No-Chicken/Power-Pico/software/bootloader/Core/Src/main.c

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
/* Includes ------------------------------------------------------------------*/
#include "main.h"
#include "crc.h"
#include "i2c.h"
#include "spi.h"
#include "tim.h"
#include "usb_device.h"
#include "gpio.h"

/* USER CODE BEGIN Includes */
#include <string.h>
#include <stdio.h>
#include "menu.h"
#include "common.h"
#include "delay.h"
#include "lcd.h"
#include "lcd_init.h"
#include "key.h"
#include "BL24C02.h"
/* USER CODE END Includes */


/* USER CODE BEGIN PV */

extern pFunction Jump_To_Application;
extern uint32_t JumpAddress;

/* USER CODE END PV */

void SystemClock_Config(void);
/* USER CODE BEGIN 0 */
void Bootloader_Main(void)
{
  // Bootloader 循环等待上位机指令
  while (1)
  {
      // 1. 发送握手信号
      USB_PutString("##PICO_BOOT##\r\n");
      // 2. 在延时期间(比如500ms)不断检查有没有收到数据
      // 这样既实现了延时，又不会阻塞接收
      uint8_t key = 0;
      for (int i = 0; i < 50; i++)
      {
          // USB_KeyPressed 应该是一个非阻塞检查函数
          // 如果收到数据返回 1，否则返回 0
          if (USB_KeyPressed(&key))
          {
              if (key == '0')
              {
                  // 收到 '0'，进入菜单
                  Main_Menu();
              }
          }
          HAL_Delay(10); // 每次只延时 10ms，检查 50 次 = 500ms
      }
  }
}
/* USER CODE END 0 */

/**
  * @brief  The application entry point.
  * @retval int
  */
int main(void)
{

  /* USER CODE BEGIN 1 */
	SCB->VTOR = FLASH_BASE;
  /* USER CODE END 1 */

  /* MCU Configuration--------------------------------------------------------*/

  /* Reset of all peripherals, Initializes the Flash interface and the Systick. */
  HAL_Init();

  /* Configure the system clock */
  SystemClock_Config();

  /* Initialize all configured peripherals */
  MX_GPIO_Init();
  MX_SPI2_Init();
  MX_TIM1_Init();
  MX_I2C1_Init();
  MX_USB_DEVICE_Init();
  MX_CRC_Init();
  /* USER CODE BEGIN 2 */

	//sys delay
	delay_init();

  //key_boot
	Key_Port_Init();

	// PWM Start for LCD backlight
	HAL_TIM_PWM_Start(&htim1, TIM_CHANNEL_3);

	//lcd
	LCD_Init();
	LCD_Fill(0, 0, LCD_W, LCD_H, BLACK);
	delay_ms(10);
	LCD_Set_Light(50);

	// extern eeprom BL24C02
	uint8_t update_flag = 0;
	if(!EEPROM_Init_Check()) {
		update_flag = EEPROM_UpdateCommand_Check();
		if(EEPROM_UpdateCommand_Check()) {
			USB_PutString("enter firmware update mode\r\n");
			EEPROM_UpdateCommand_Write(false);
		}
	}

  // 开机启动时如果按下KEY, 或EEPROM有升级标志, 进入boot中IAP升级模式
  if(HAL_GPIO_ReadPin(KEYB_PORT, KEYB_PIN) == 0 || update_flag)
  {
		// 延时判断是否真的按下
    delay_ms(500);
    if(HAL_GPIO_ReadPin(KEYB_PORT, KEYB_PIN) == 0 || update_flag)
    {
      LCD_ShowString(72, LCD_H/3, (uint8_t*)"Bootload", WHITE, BLACK, 24, 0);//12*6,16*8,24*12,32*16
      FLASH_If_Init();
      Bootloader_Main();
    }
  }

  // 如果没按下KEY1, 且有APP程序, 则运行APP, 没有APP则
  else
  {
    UpgradeInfo_t app_info;

    // 1. 从独立的校验区(Sector 3)读取升级信息结构体
    memcpy(&app_info, (void*)UPGRADE_INFO_ADDRESS, sizeof(UpgradeInfo_t));

    // 2. 检查标志是否有效 (魔法字和完成状态)
    if (app_info.magic_word == MAGIC_WORD && app_info.upgrade_status == UPGRADE_STATUS_COMPLETE)
    {
        // 3. 校验APP固件的完整性
        uint32_t current_crc = Calculate_CRC32(APPLICATION_ADDRESS, app_info.new_app_size);

        if (current_crc == app_info.new_app_crc32)
        {
            // 4. 校验成功，执行跳转
            USB_PutString("Valid APP found, jumping to application...\r\n");
            jump_to_app();
        }
    }
		// no legal APP
		else
		{
      USB_PutString("No App found, enter firmware update mode\r\n");
			LCD_ShowString(74, LCD_H/3, (uint8_t*)"No App!", WHITE, BLACK, 24, 0);//12*6,16*8,24*12,32*16
      LCD_ShowString(24, LCD_H/3+48, (uint8_t*)"Plz Download APP", WHITE, BLACK, 24, 0);
			HAL_Delay(2000);
			LCD_ShowString(72, LCD_H/3, (uint8_t*)"Bootload", WHITE, BLACK, 24, 0);//12*6,16*8,24*12,32*16
      FLASH_If_Init();
      Bootloader_Main();
		}
  }


  /* USER CODE END 2 */

  /* Infinite loop */
  /* USER CODE BEGIN WHILE */
  while (1)
  {
    /* USER CODE END WHILE */

    /* USER CODE BEGIN 3 */
		HAL_Delay(500);
  }
  /* USER CODE END 3 */
}

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
